THEzenith1/Multipad/CAD Exports/M1_FrontHousingKeyholder.step

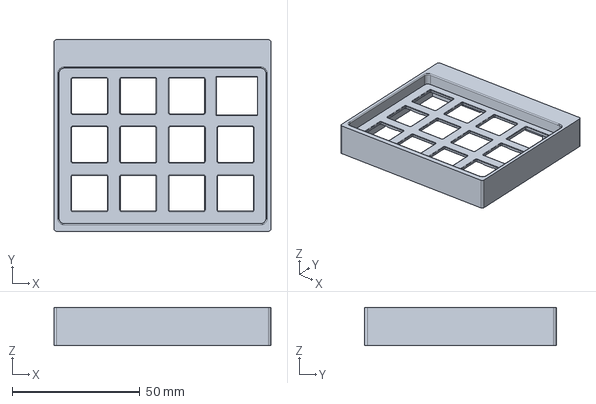
[picture p15: CAD file, 2026-06-11]
CAD Exports/M1_FrontHousingKeyholder.step
85.0 x 75.0 x 15.0 mm
