THEzenith1/Multipad/CAD Exports/S1_BottomPlate.step

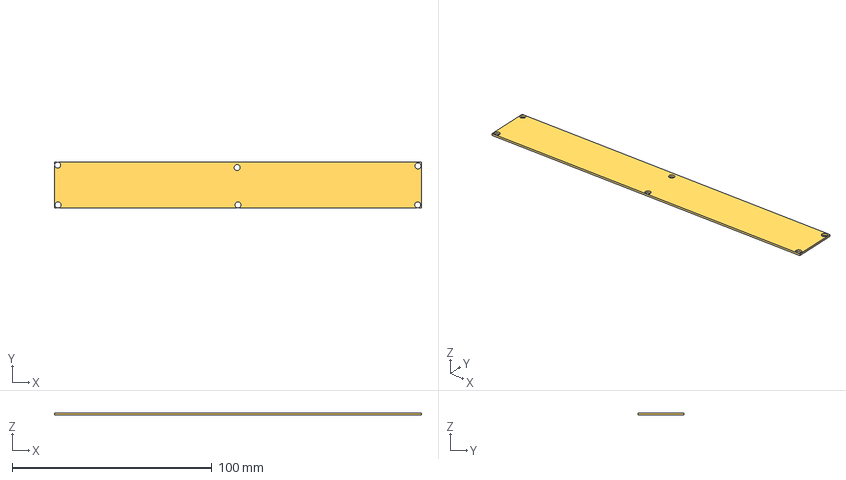
[picture p16: CAD file, 2026-06-11]
CAD Exports/S1_BottomPlate.step
184.0 x 23.0 x 1.00 mm
