THEzenith1/Multipad/CAD Exports/M2_FrontHousing.step

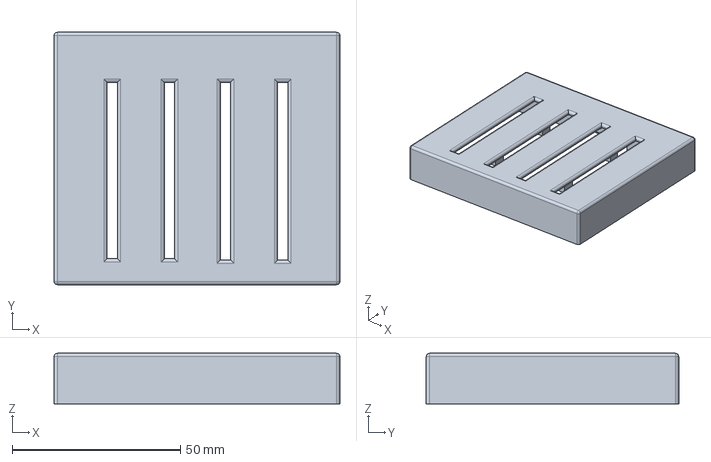
[picture p17: CAD file, 2026-06-11]
CAD Exports/M2_FrontHousing.step
85.0 x 75.0 x 15.0 mm
