THEzenith1/Multipad/CAD Exports/M4_WheelBaseplate.step

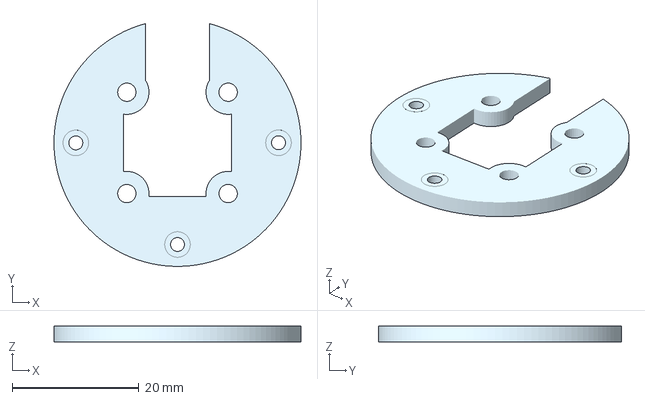
[picture p18: CAD file, 2026-06-11]
CAD Exports/M4_WheelBaseplate.step
39.0 x 38.3 x 2.50 mm
